DawidAntosz/TwoWheelRobot/src/TwoWheelRobot_arduino/data/assets/robot.png

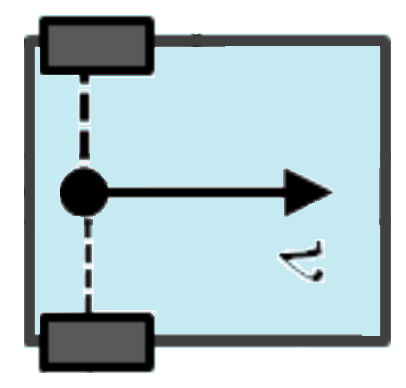
src/TwoWheelRobot_arduino/data/assets/robot.png
